lishen2/ProgrammableLED/software/src/display_state.h

#ifndef _DISPLAY_STATE_H_
#define _DISPLAY_STATE_H_

enum DISPLAY_STATE
{
	STATE_BREAK_LIGHT,
    STATE_GRADIENTER,
	STATE_COLORLIGHT,
	STATE_MAX,
};

void STATE_Init(void);
void STATE_NextState(void);
void STATE_SetState(enum DISPLAY_STATE state);

#endif
