lishen2/ProgrammableLED/software/src/power.c

#include "stm32f10x.h"
#include "utils.h"
#include "led.h"
#include "xl345.h"
#include "power.h"

/* set all unused pin */
void PWR_SetUnusedPin(void)
{
    GPIO_InitTypeDef GPIO_InitStructure;
    
    RCC_APB2PeriphClockCmd(RCC_APB2Periph_GPIOA | RCC_APB2Periph_GPIOB, ENABLE);  

	GPIO_InitStructure.GPIO_Speed = GPIO_Speed_2MHz;
	GPIO_InitStructure.GPIO_Mode = GPIO_Mode_IPD;

    /* GPIOA */
    GPIO_InitStructure.GPIO_Pin = GPIO_Pin_1 | GPIO_Pin_2 | GPIO_Pin_4 | 
                                  GPIO_Pin_8 | GPIO_Pin_9 | GPIO_Pin_10 |
								  GPIO_Pin_11 | GPIO_Pin_12;
	GPIO_Init(GPIOA, &GPIO_InitStructure);

    /* GPIOB */
    GPIO_InitStructure.GPIO_Pin = GPIO_Pin_1 | GPIO_Pin_5 | GPIO_Pin_9 | 
                                  GPIO_Pin_10 | GPIO_Pin_11;
	GPIO_Init(GPIOB, &GPIO_InitStructure);

    
    return;
}

void PWR_LowPower(void)
{   
	LED_SetColor(0x00);
	
    LED_PowerOff();

    /* enter stop mode */
    PWR_EnterSTOPMode(PWR_Regulator_LowPower, PWR_STOPEntry_WFI);
    
    return;
}

void PWR_Restore(void)
{        
    LED_PowerOn();
    
    return;
}
